johnwinans/2057-ICE40HX4K-TQ144-breakout/verilog/minimal/tb.v

`timescale 1ns/1ps

module tb();

	reg clk;		// the free running clock

	top uut (
		.btn1(clk)
		// don't need to connect every signal here if not want to
		);

	initial begin
		$dumpfile("tb.vcd");		// where to write the dump
		$dumpvars;					// dump EVERYTHING
		clk = 0;
	end
	
	always #1 clk = ~clk;

	initial begin
		#1000;
		//#16000000;
		$finish;
	end

endmodule
